kraemerlukas314/A-tiny-bike-sentry/src/main/Gpio.h

/**
 * @file Gpio.h
 *
 * Header file for Gpio class
 *
 * @author Lukas Krämer
 */
#pragma once

#include "Arduino.h"
#include "Timing.h"
#include "defines.h"

/**
 * Gpio class that provides
 * functions for direct hardware actions (e.g. turning on/off digital pins)
 *
 */
class Gpio {
   public:
    Gpio();
    void setup();
    void on(byte pin);
    void off(byte pin);
    void set_pin(byte pin, bool state);
    void toggle(byte pin, int iterations, long d);

   private:
    Timing timing;  ///< Timing instance
};
